2025-SSR-Team5/KiCadData/maincircuit/FreeCadData/ESP32.FCStd

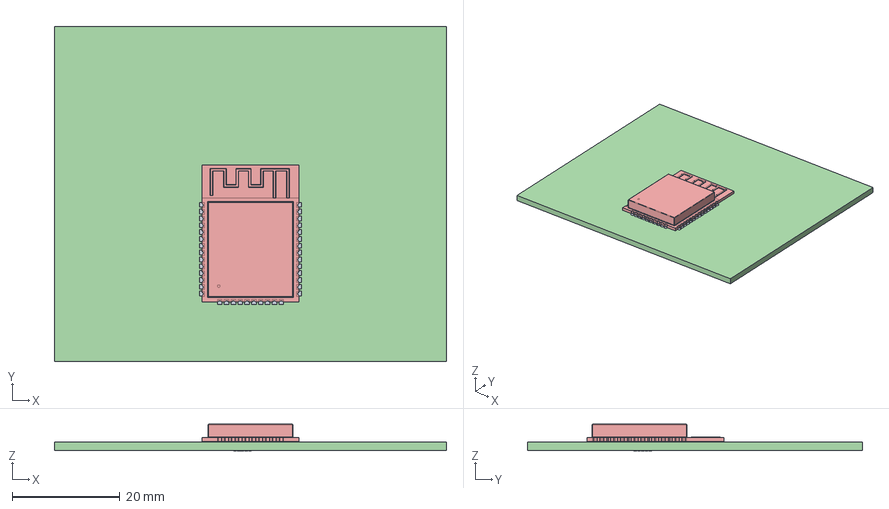
[picture p15: CAD file, 2025-08-02]
maincircuit/FreeCadData/ESP32.FCStd
72.8 x 62.3 x 4.93 mm
topPads
btmPads
TH-Drills
PCB
