2025-SSR-Team5/KiCadData/maincircuit/FreeCadData/MA10EB045.stp

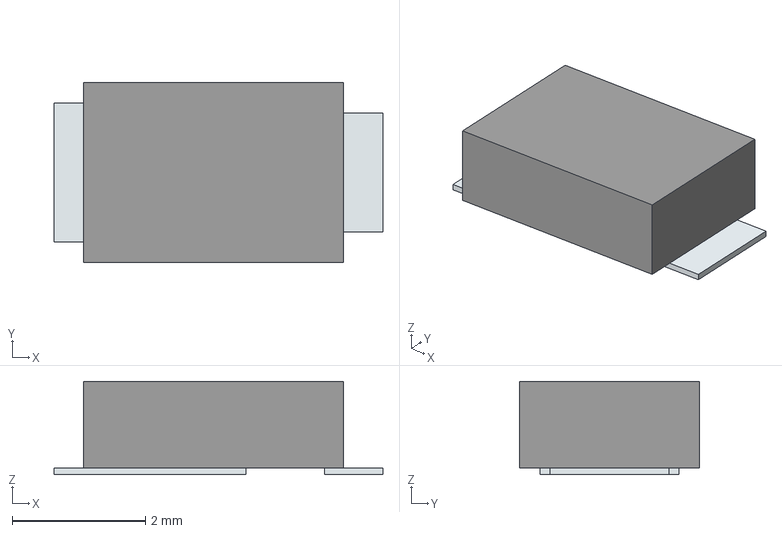
[picture p16: CAD file, 2025-08-02]
maincircuit/FreeCadData/MA10EB045.stp
4.93 x 2.70 x 1.40 mm
Pins
