2025-SSR-Team5/KiCadData/maincircuit/FreeCadData/ZH_B6B.FCStd

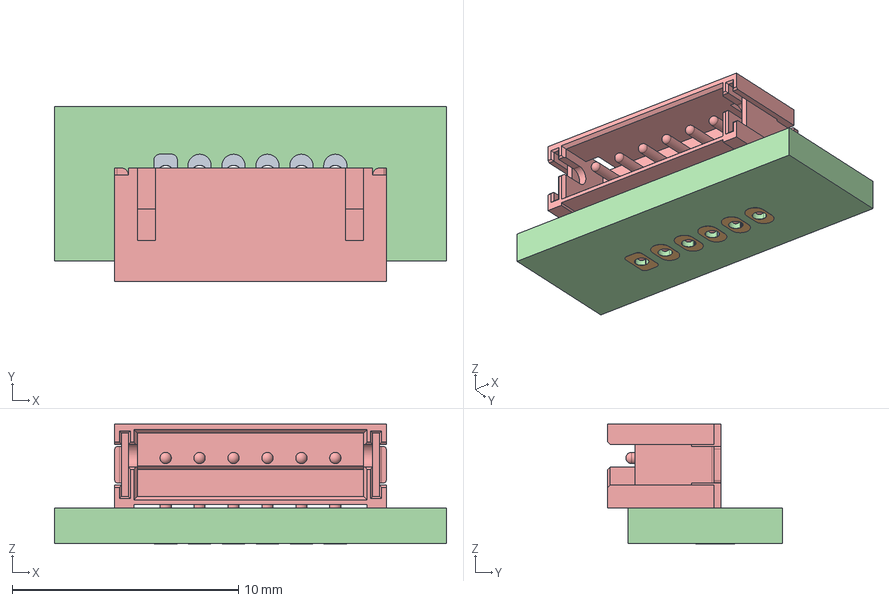
[picture p17: CAD file, 2025-08-02]
maincircuit/FreeCadData/ZH_B6B.FCStd
17.3 x 7.71 x 5.30 mm
topPads
btmPads
TH-Drills
PCB
ZH_Connector_SMT_Top
