2025-SSR-Team5/KiCadData/maincircuit/FreeCadData/2SC3325.step

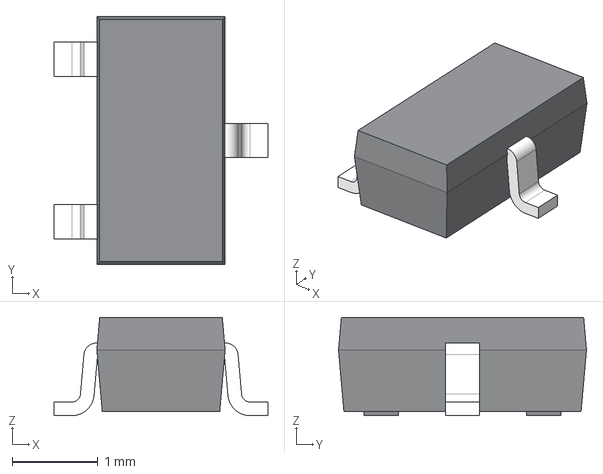
[picture p18: CAD file, 2025-07-13]
maincircuit/FreeCadData/2SC3325.step
2.50 x 2.90 x 1.15 mm
