2025-SSR-Team5/KiCadData/maincircuit/FreeCadData/5077CR-16SMC2-BK-TR019.step

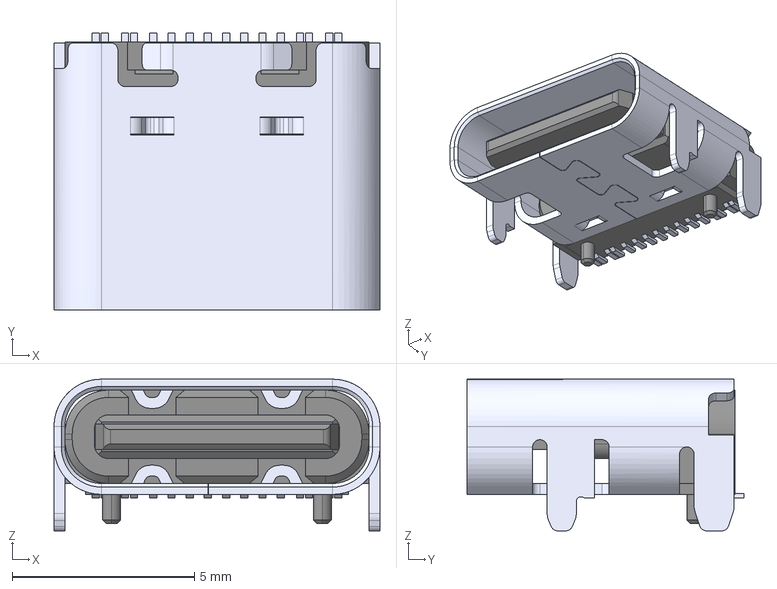
[picture p19: CAD file, 2025-07-13]
maincircuit/FreeCadData/5077CR-16SMC2-BK-TR019.step
8.94 x 7.60 x 4.16 mm
